va7deo/MegaSys1_A/rtl/sdram/jtframe_romrq.v

/*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
    Author: Jose Tejada Gomez. Twitter: @topapate
    Version: 1.0
    Date: 28-2-2019 */

// The best use case is with addr_ok going down and up for each addr change
// but it works too with addr_ok permanently high as long as addr input is
// not changed until the data_ok signal is produced. If the requester cannot
// guarantee that, it should toggle addr_ok for each request

// LATCH LATENCY Timing Requirements
//    0     1    medium
//    1     2    easy

module jtframe_romrq #(parameter
    SDRAMW  = 22,  // SDRAM width
    AW      = 18,
    DW      =  8,
    OKLATCH =  1,  // Set to 1 to latch the data_ok signal. This implies that
                   // data_ok will be high for one clock cycle after the input address
                   // has changed. The requesting module needs to take care of that
                   // If OKLATCH is zero, data_ok is combinational and it will go to
                   // zero as soon as the input address changes. This simplifies the
                   // requesting logic but it is more demanding for timing constraints
    DOUBLE  =  0,

    LATCH   =  0  // dout is latched
)(
    input               rst,
    input               clk,

    input               clr, // clears the cache
    input [SDRAMW-1:0]  offset,

    // <-> SDRAM
    input [15:0]        din,
    input               din_ok,
    input               dst,
    input               we,
    output reg          req,
    output [SDRAMW-1:0] sdram_addr,

    // <-> Consumer
    input [AW-1:0]      addr,
    input               addr_ok,    // signals that value in addr is valid
    output              data_ok,    // strobe that signals that data is ready
    output reg [DW-1:0] dout
);

reg [AW-1:0] addr_req;

reg [AW-1:0] cached_addr0, cached_addr1, addr_l;
reg [31:0]   cached_data0, cached_data1;
reg [1:0]    good;
reg          hit0, hit1;
reg          dend, double, cache_ok;
wire [AW-1:0] shifted;

assign sdram_addr = offset + { {SDRAMW-AW{1'b0}}, addr_req>>(DW==8)};
assign data_ok    = OKLATCH ? cache_ok : addr_ok && ( hit0 || hit1 );

always @(*) begin
    case(DW)
        8:  addr_req = {addr[AW-1:2],2'b0};
        16: addr_req = {addr[AW-1:1],1'b0};
        32: addr_req = addr;
    endcase
    // It is important to leave === for simulations, instead of ==
    // It shouldn't have any implication for synthesis
    hit0 = addr_req === cached_addr0 && good[0];
    hit1 = addr_req === cached_addr1 && good[1];
    req = (!(hit0 || hit1) && !we) && addr_ok;
end

// reg [1:0] ok_sr;

always @(posedge clk, posedge rst) begin
    if( rst ) begin
        good         <= 'd0;
        cached_data0 <= 'd0;
        cached_data1 <= 'd0;
        cached_addr0 <= 'd0;
        cached_addr1 <= 'd0;
        cache_ok     <= 0;
        dend         <= 0;
        double       <= 0;
    end else begin
        if( clr ) good <= 0;
        if( req ) addr_l <= addr_req;
        if( we ) begin
            if( dst | (double&~dend) ) begin
                cached_data1 <= cached_data0;
                cached_addr1 <= cached_addr0;
                cached_data0[31:16] <= din;
                if( double )
                    cached_addr0[1] <= ~cached_addr0[1];
                else
                    cached_addr0 <= addr_l;
                good <= { good[0], 1'b1 };
                dend <= 1;
            end
            if( dend ) begin
                cached_data0[31:16] <= din;
                cached_data0[15: 0] <= cached_data0[31:16];
                if( !LATCH[0] && !DOUBLE[0] ) cache_ok<= 1;
                if( DOUBLE ) double <= ~double;
                dend <= 0;
            end
        end
        else begin
            cache_ok <= addr_ok && ( hit0 || hit1 );
            double   <= 0;
        end
    end
end

// data_mux selects one of two cache registers
// but if we are getting fresh data, it selects directly the new data
// this saves one clock cycle at the expense of more LUTs
wire [31:0] data_mux = hit0 ? cached_data0 : cached_data1;
reg  [DW-1:0] preout;

generate
    if(DW==8) begin
        always @(*)
        case( addr[1:0] )
            2'd0: preout = data_mux[ 7: 0];
            2'd1: preout = data_mux[15: 8];
            2'd2: preout = data_mux[23:16];
            2'd3: preout = data_mux[31:24];
        endcase
    end else if(DW==16) begin
        always @(*)
        case( addr[0] )
                1'd0: preout = data_mux[15:0];
                1'd1: preout = data_mux[31:16];
        endcase
    end else always @(*) preout = data_mux;
endgenerate

generate
    if( LATCH==0 ) begin : data_latch
        always @(*) dout = preout;
    end else begin : no_data_latch
        always @(posedge clk) dout <= preout;
    end
endgenerate

`ifdef JTFRAME_SDRAM_STATS
jtframe_romrq_stats u_stats(
    .clk    ( clk       ),
    .rst    ( rst       ),
    .req    ( req       ),
    .we     ( we        ),
    .din_ok ( din_ok    ),
    .data_ok( data_ok   )
);
`endif

`ifdef SIMULATION
`ifndef VERILATOR
`ifndef JTFRAME_SIM_ROMRQ_NOCHECK
reg [AW-1:0] last_addr;
reg          waiting, last_req;

always @(posedge clk, posedge rst) begin
    if( rst ) begin
        waiting <= 0;
        last_req <= 0;
    end else begin
        last_req <= req;
        if( req && !last_req ) begin
            if( waiting ) begin
                $display("ERROR: %m new request without finishing the previous");
                $finish;
            end
            last_addr <= addr;
            waiting <= 1;
        end
        if( din_ok && we ) waiting <= 0;
        if( waiting && !addr_ok ) begin
            $display("ERROR: %m data request interrupted");
            $finish;
        end
        if( addr != last_addr && addr_ok) begin
            if( waiting ) begin
                $display("ERROR: %m address changed at time %t",$time);
                #40 $finish;
            end else waiting <= !hit0 && !hit1;
        end
    end
end
`endif
`endif
`endif

endmodule // jtframe_romrq

`ifdef JTFRAME_SDRAM_STATS
////////////////////////////////////////////////////////////////
module jtframe_romrq_stats(
    input clk,
    input rst,
    input req,
    input we,
    input din_ok,
    input data_ok
);

// latency data
integer cur, longest, shortest, total, acc_cnt;
reg cnt_en, last_req, first;

always @(posedge clk, posedge rst) begin
    if( rst ) begin
        cur      <= 0;
        longest  <= 0;
        shortest <= 10000;
        cnt_en   <= 0;
        last_req <= 0;
        acc_cnt  <= 0;
        total    <= 0;
        first    <= 1;
    end else begin
        last_req <= req;
        if(req && !last_req) begin
            cur <= 1;
            cnt_en <= 1;
            acc_cnt <= acc_cnt+1;
        end
        if( cnt_en ) begin
            cur <= cur+1;
            if( (we && din_ok) || data_ok ) begin
                if( !first ) begin
                    if(cur>longest) longest <= cur;
                    if(cur<shortest) shortest <= cur;
                    total <= total + cur;
                end
                first  <= 0;
                cnt_en <= 0;
            end
        end
    end
end

initial begin
    forever begin
        /* verilator lint_off STMTDLY */
        #16_666_667;
        /* verilator lint_on STMTDLY */
        if( !first )
            $display("Latency %m %2d - %2d - %2d",
                shortest, total/acc_cnt, longest );
    end
end

endmodule
`endif
