va7deo/MegaSys1_A/rtl/mem/cache.v

///----------------------------------------------------------------------------
//
//  Copyright 2022 Darren Olafson
//
//  MiSTer Copyright (C) 2017 Sorgelig
//
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
//----------------------------------------------------------------------------


// simple read-only cache 
// specificly for 68k program rom.  todo - parameterize 
module cache
(
    input reset,
    input clk,

    input cache_req,
    input [17:0] cache_addr,

    output cache_valid,
    output [15:0] cache_data,

    input  [15:0] rom_data,
    input  rom_valid,
    
    output reg rom_req,
    output [17:0] rom_addr
);


reg  [17:9] tag [511:0];
reg [511:0] valid ;
reg   [1:0] state = 0;

reg   [8:0] idx_r;
wire  [8:0] idx = cache_addr[8:0];

wire hit;

// if tag value matches the upper bits of the address 
// and valid then no need to pass request to sdram 
assign hit = ( tag[idx] == cache_addr[17:9] && valid[idx] == 1 );


assign cache_data  = ( hit == 1 ) ? cache_dout : ( (state == 1 && rom_valid == 1) ? rom_data : cache_din );
assign cache_valid = ( cache_req == 1 ) && ( hit == 1 || rom_valid == 1 );

assign rom_addr = cache_addr;

always @ (posedge clk) begin
    
    if ( reset == 1 ) begin
        state <= 0;
        // reset bits that indicate tag is valid
        valid <= 0;
    end else begin
        // if no read request then do nothing
        if ( cache_req == 0 ) begin
            rom_req <= 0;
            state   <= 0;
        end else begin
            // if there is a hit then read from cache and say we are done
            if ( hit == 1 ) begin
                rom_req <= 0;
                state   <= 0;
            end else if ( state == 0 ) begin
                // read from memory

                idx_r <= idx;
                
                // we need to read from sdram
                rom_req <= 1;

                // next state is wait for rom ready
                state <= 1;
                
            end else if ( state == 1 && rom_valid == 1 ) begin

                // write updated tag
                tag[idx_r] <= rom_addr[17:9];
                // mark tag valid
                valid[idx_r] <= 1'b1;

                cache_din <= rom_data;
                rom_req <= 0;
                
                state <= 2;
            end else if ( state == 2 ) begin
                // write complete
                state <= 0;
            end
        end
    end
end

reg  [15:0] cache_din;
wire [15:0] cache_dout;

dual_port_ram #(.LEN(512), .DATA_WIDTH(16)) prog_cache
(
    .clock_a( clk ),
    .address_a( idx_r ),
    .wren_a( state == 2 ),
    .data_a( cache_din ),
    .q_a( ),
    
    .clock_b( clk ),
    .address_b( idx ),  
    .wren_b( 0 ),
    .data_b( ),
    .q_b( cache_dout )    
);

endmodule
